jbmorley/little-luggable/manufacture/keyboard-switch-collar.stl

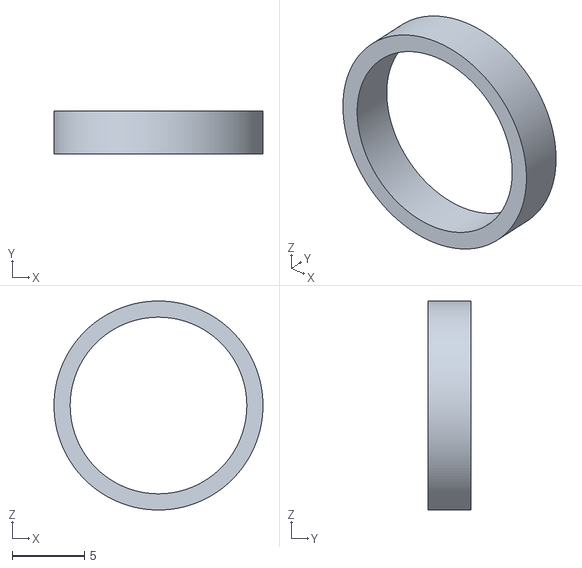
[picture p15: CAD file, 2023-02-21]
manufacture/keyboard-switch-collar.stl
14.5 x 3.00 x 14.5
