jbmorley/little-luggable/manufacture/keyboard-usb-port-collar.stl

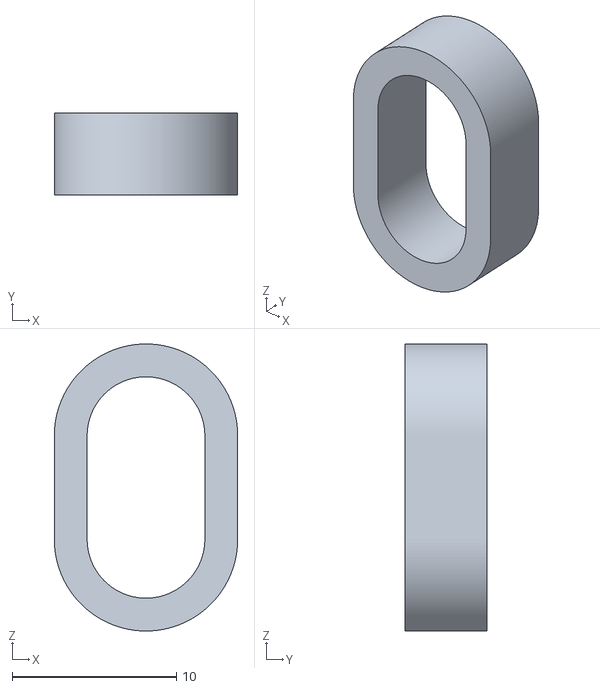
[picture p16: CAD file, 2023-02-21]
manufacture/keyboard-usb-port-collar.stl
11.2 x 5.00 x 17.5
