jbmorley/little-luggable/manufacture/keyboard-mounting-bracket-bottom-right.stl

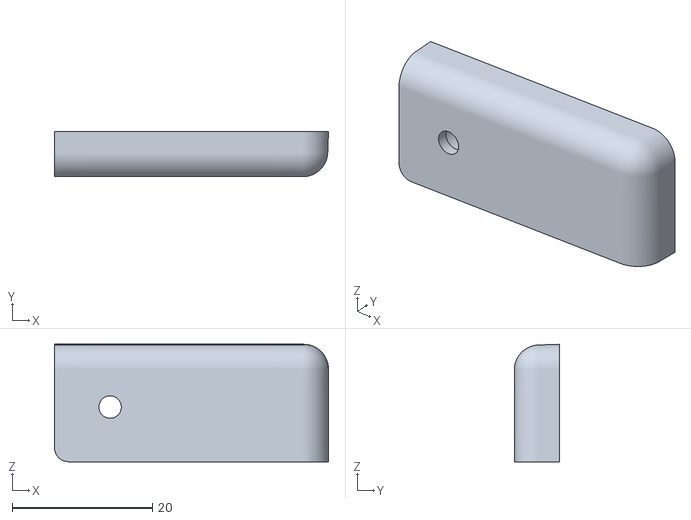
[picture p17: CAD file, 2023-02-21]
manufacture/keyboard-mounting-bracket-bottom-right.stl
39.1 x 6.47 x 16.8
