jbmorley/little-luggable/manufacture/keyboard-mounting-bracket-top-right.stl

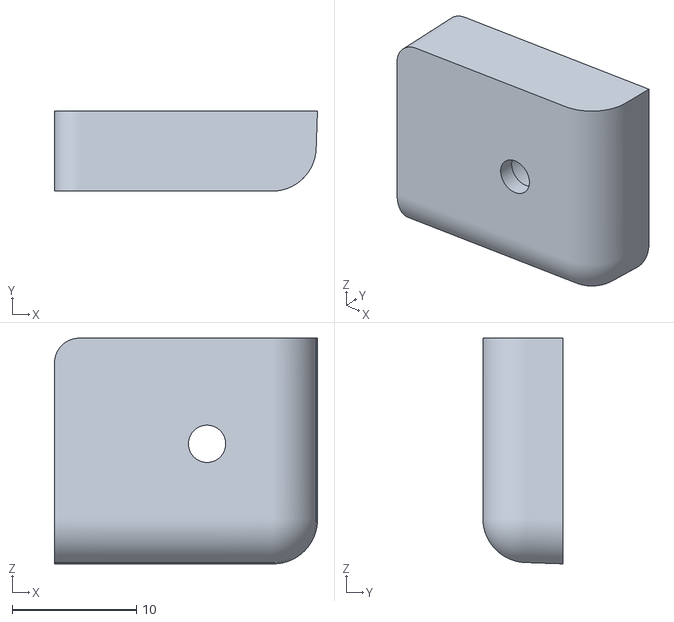
[picture p18: CAD file, 2023-02-12]
manufacture/keyboard-mounting-bracket-top-right.stl
21.2 x 6.47 x 18.2
