jbmorley/little-luggable/manufacture/keyboard-mounting-bracket-top-left.stl

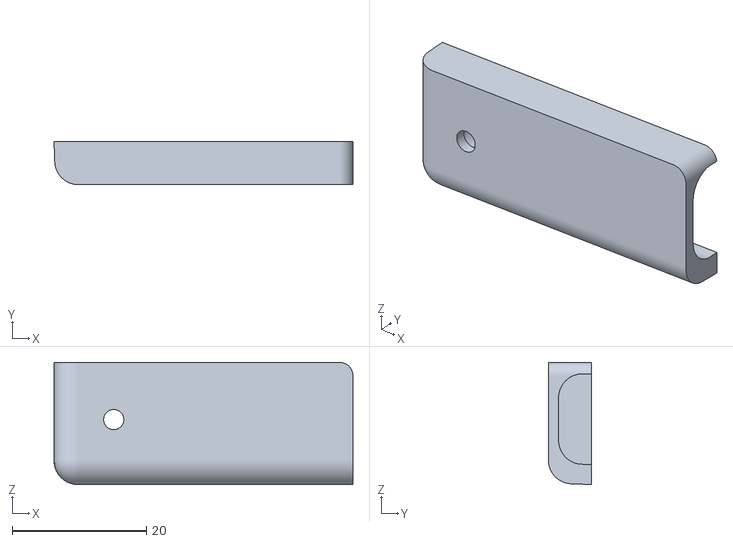
[picture p19: CAD file, 2023-02-12]
manufacture/keyboard-mounting-bracket-top-left.stl
44.5 x 6.47 x 18.2
