jbmorley/little-luggable/manufacture/keyboard-pcb.dxf

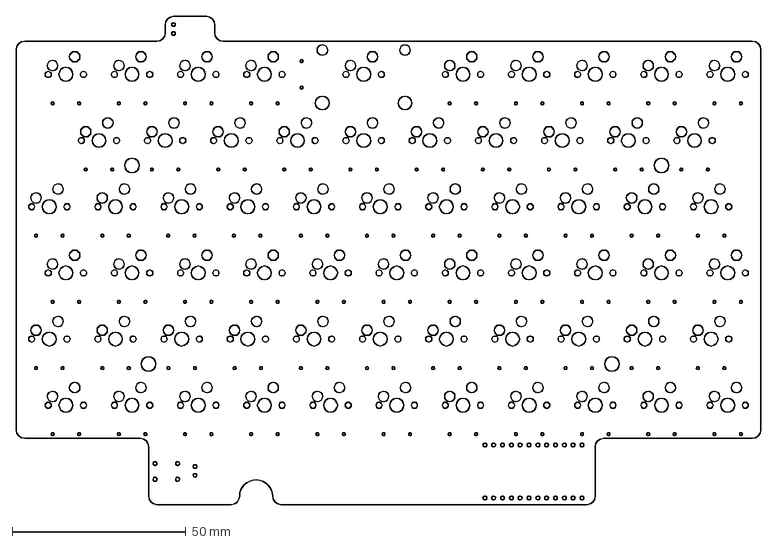
[picture p20: CAD file, 2023-02-05]
manufacture/keyboard-pcb.dxf
214.3 x 140.5 mm
