jbmorley/little-luggable/manufacture/back.dxf

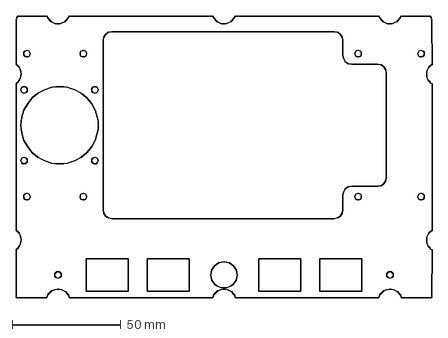
[picture p21: CAD file, 2023-01-06]
manufacture/back.dxf
191.0 x 129.2 mm
